dubpixel/dpx-Cadet_panels/gerber/fromFUSION/nfg/PANELIZED_245 v7_2021-07-21_Combined_Bottom.png

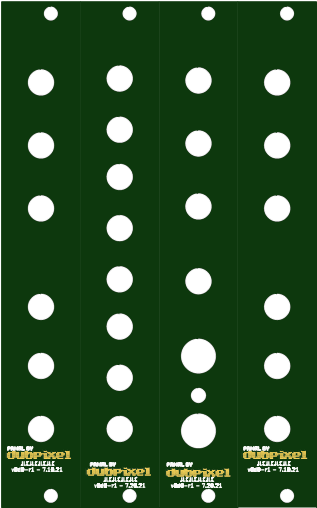
gerber/fromFUSION/nfg/PANELIZED_245 v7_2021-07-21_Combined_Bottom.png
