dubpixel/dpx-Cadet_panels/photos/PANELS_3.jpg

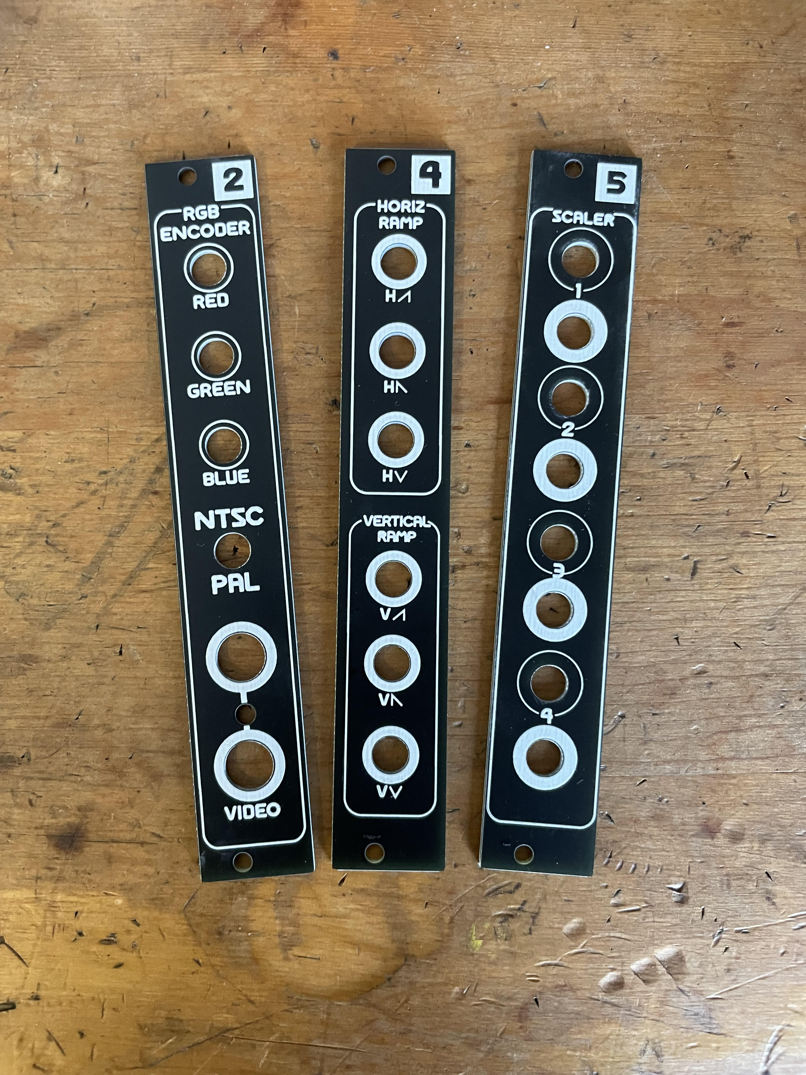
photos/PANELS_3.jpg
