dubpixel/dpx-Cadet_panels/photos/PANELS_6.jpg

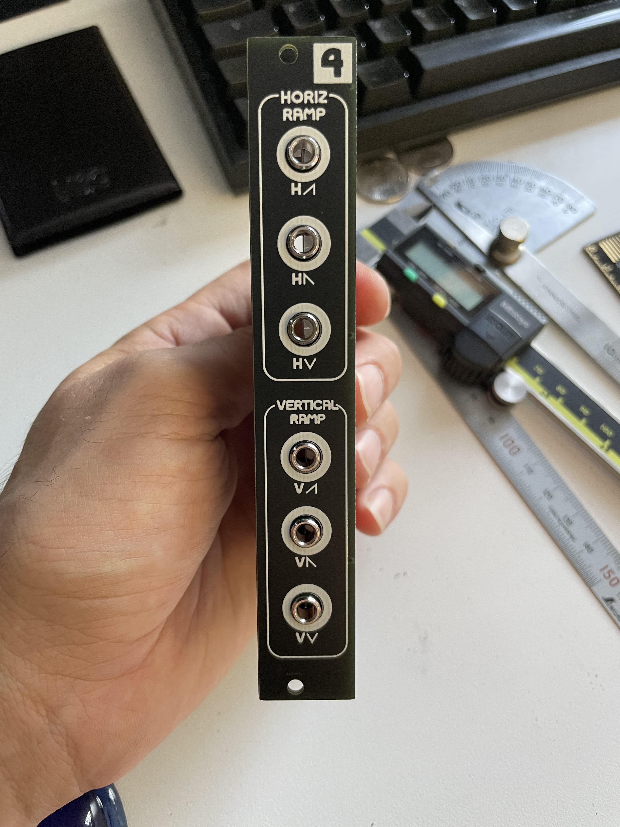
photos/PANELS_6.jpg
