dubpixel/dpx-Cadet_panels/photos/PANELS_7.jpg

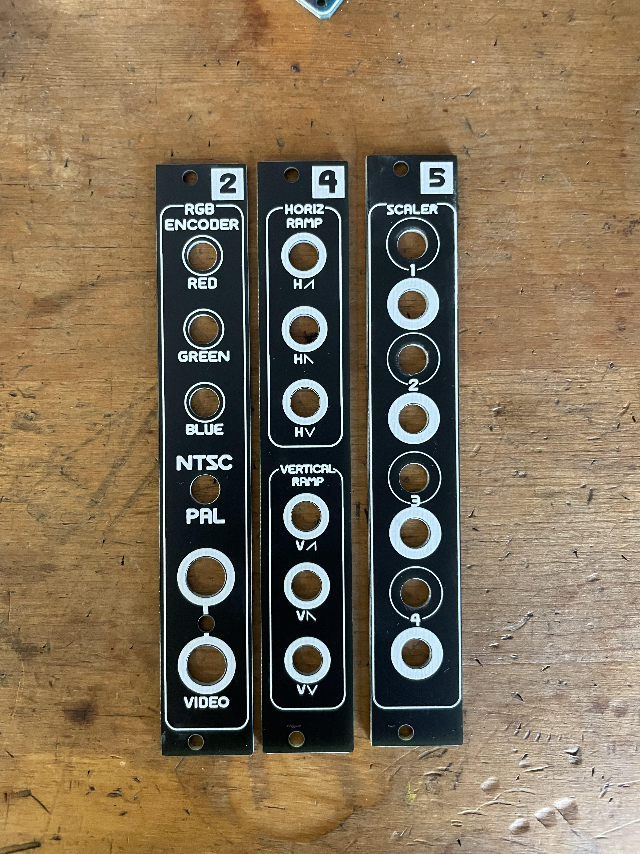
photos/PANELS_7.jpg
